simonjgreen/OpenObservatory-GardenInk/art_studio/reference/robin.png

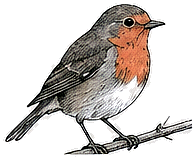
art_studio/reference/robin.png
