simonjgreen/OpenObservatory-GardenInk/design/concepts/04-selected-editorial-target.png

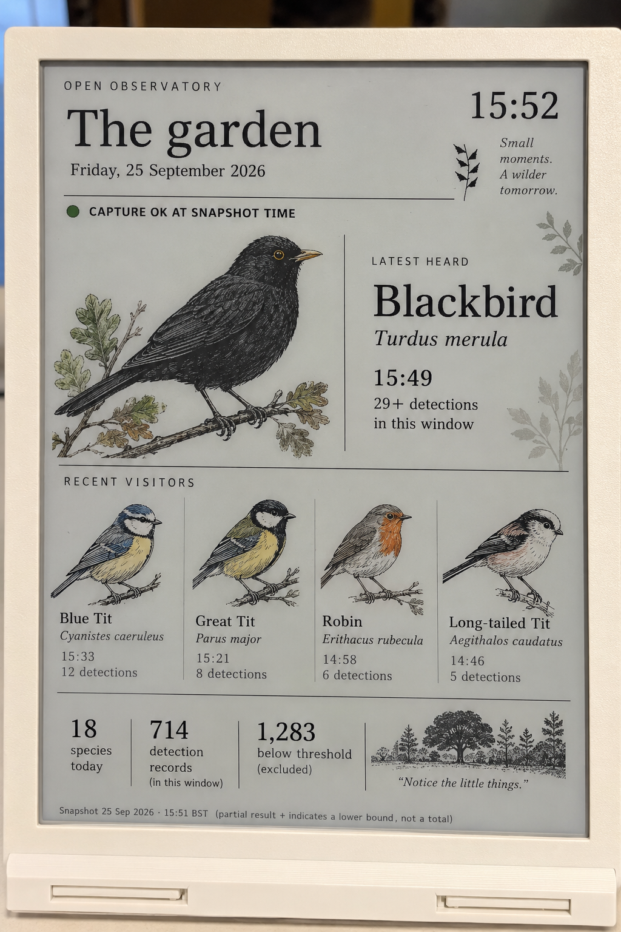
design/concepts/04-selected-editorial-target.png
