simonjgreen/OpenObservatory-GardenInk/design/concepts/after-dark-2026-09-27/01-night-rhythm.png

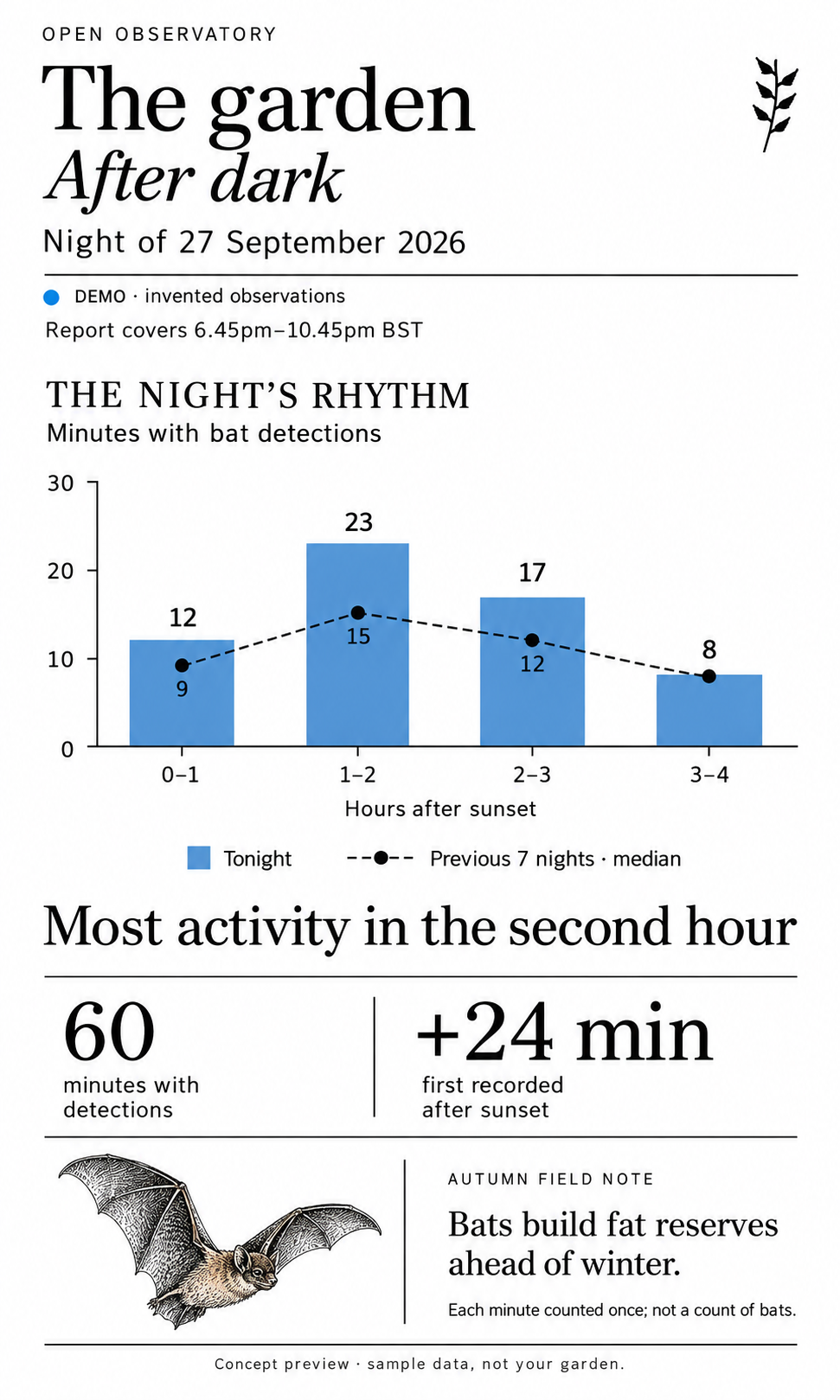
design/concepts/after-dark-2026-09-27/01-night-rhythm.png
