simonjgreen/OpenObservatory-GardenInk/design/concepts/after-dark-2026-09-27/02-seven-nights.png

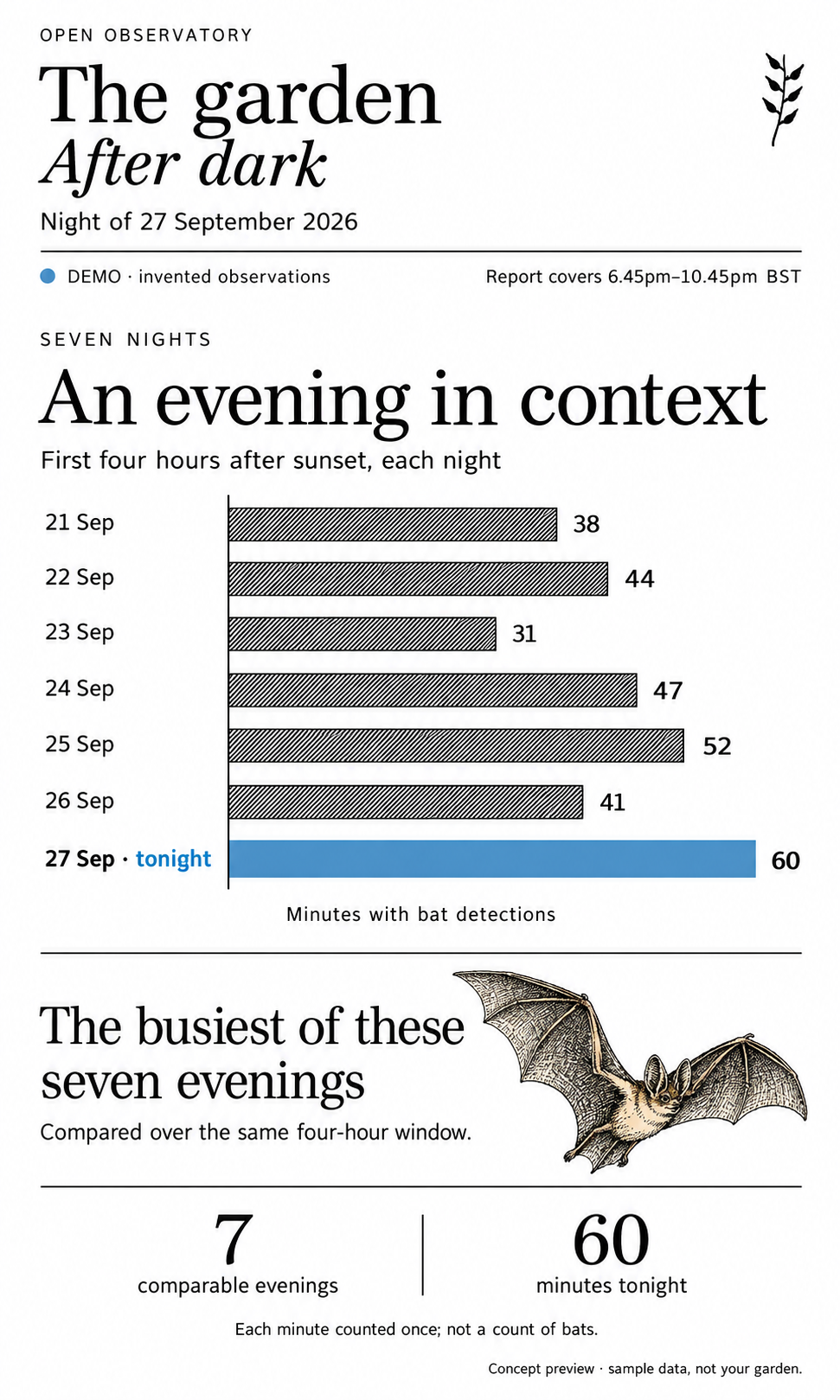
design/concepts/after-dark-2026-09-27/02-seven-nights.png
