simonjgreen/OpenObservatory-GardenInk/design/concepts/after-dark-bats-and-owls-v3/01-night-rhythm.png

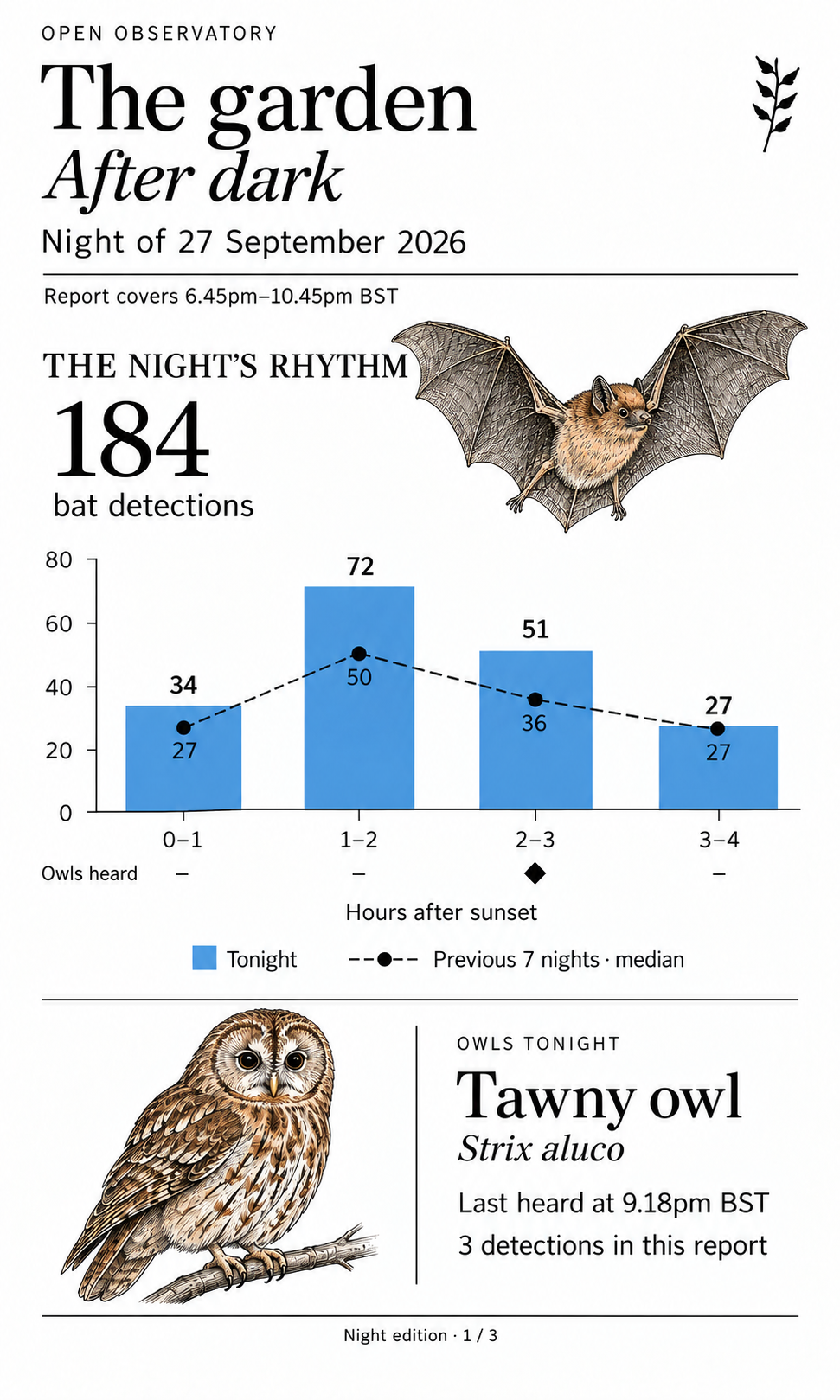
design/concepts/after-dark-bats-and-owls-v3/01-night-rhythm.png
