simonjgreen/OpenObservatory-GardenInk/design/concepts/after-dark-bats-and-owls-v3/02-seven-nights.png

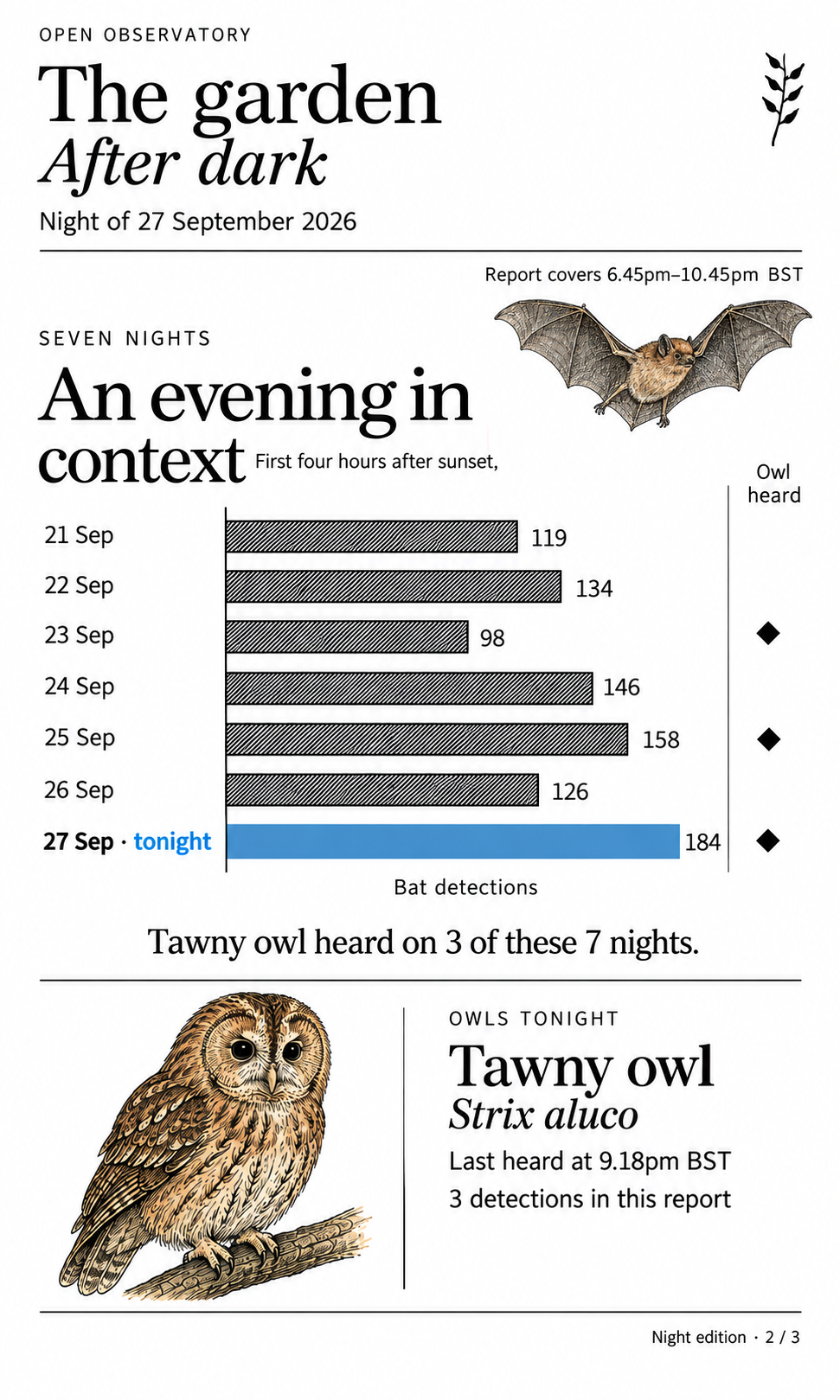
design/concepts/after-dark-bats-and-owls-v3/02-seven-nights.png
