simonjgreen/OpenObservatory-GardenInk/design/concepts/after-dark-owls-2026-09-27/01-night-rhythm-with-owl.png

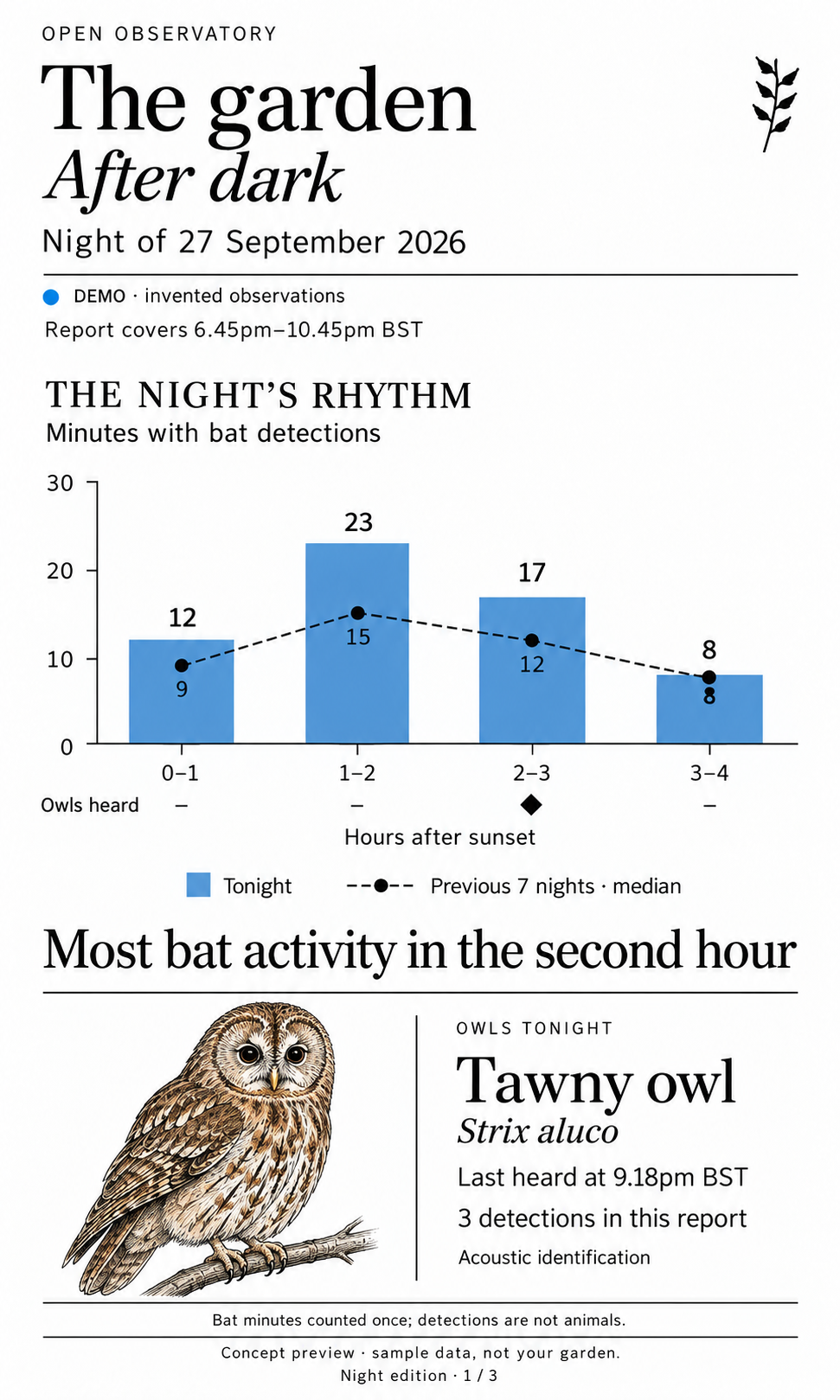
design/concepts/after-dark-owls-2026-09-27/01-night-rhythm-with-owl.png
