simonjgreen/OpenObservatory-GardenInk/design/concepts/after-dark-owls-2026-09-27/02-seven-nights-with-owl.png

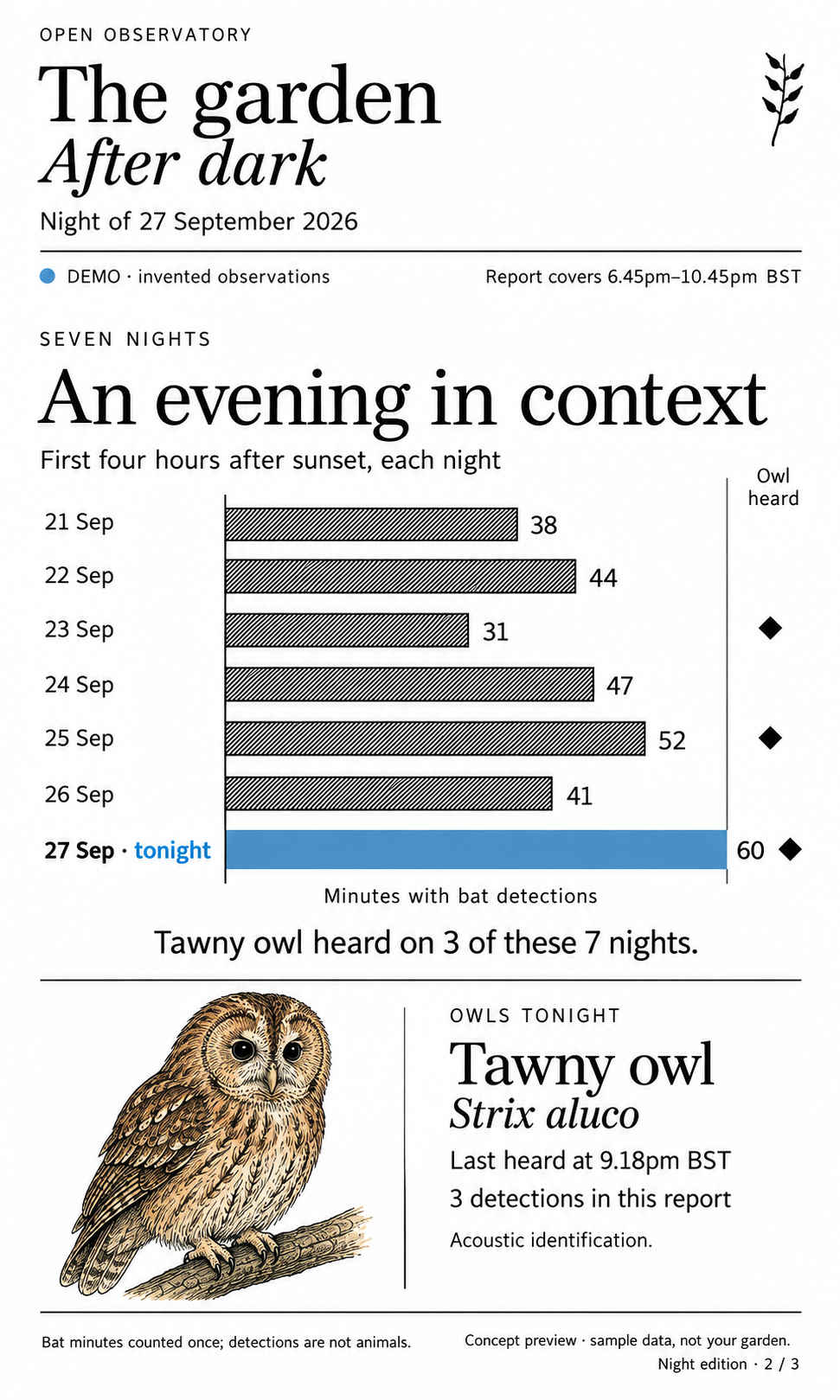
design/concepts/after-dark-owls-2026-09-27/02-seven-nights-with-owl.png
