simonjgreen/OpenObservatory-GardenInk/design/previews/after-dark/night-rhythm.png

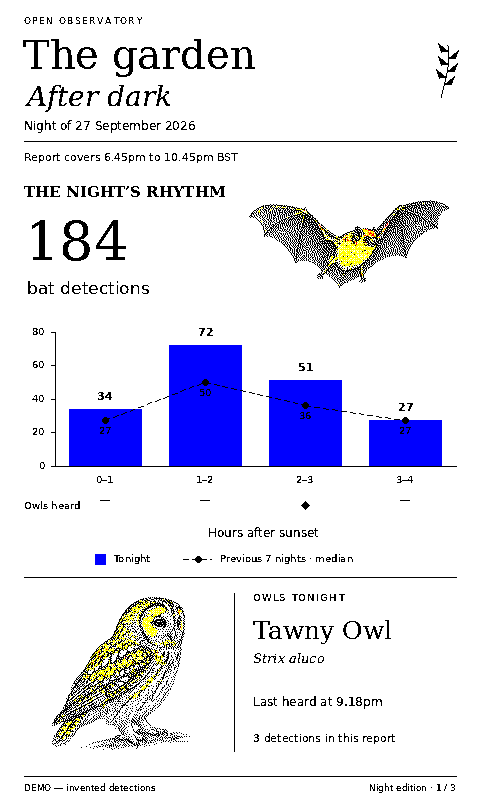
design/previews/after-dark/night-rhythm.png
