simonjgreen/OpenObservatory-GardenInk/design/previews/v2.1/no_clock.png

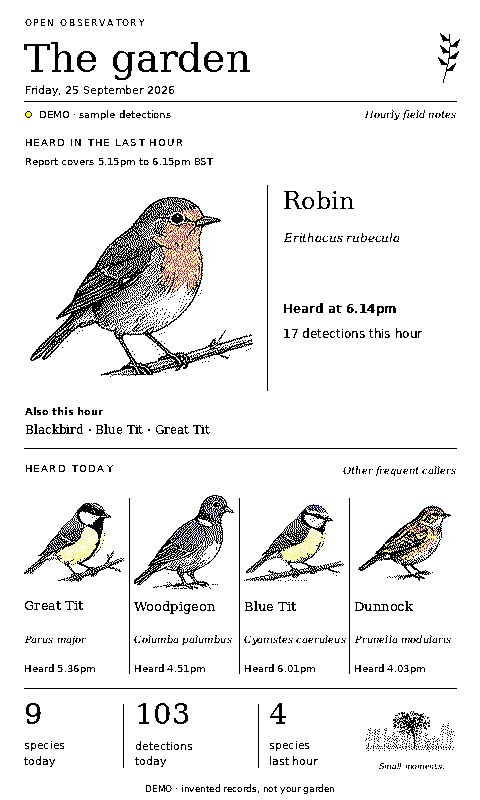
design/previews/v2.1/no_clock.png
