simonjgreen/OpenObservatory-GardenInk/display/assets/birds/aegithalos_caudatus.png

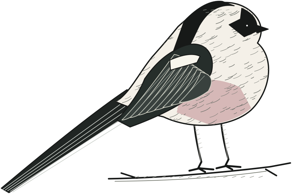
display/assets/birds/aegithalos_caudatus.png
