simonjgreen/OpenObservatory-GardenInk/display/assets/birds/alcedo_atthis.png

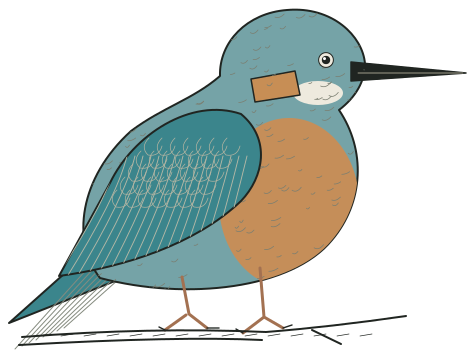
display/assets/birds/alcedo_atthis.png
