simonjgreen/OpenObservatory-GardenInk/display/assets/birds/anas_platyrhynchos.png

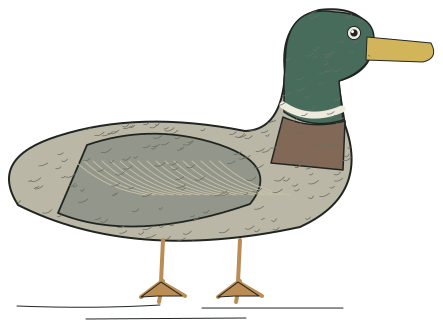
display/assets/birds/anas_platyrhynchos.png
