simonjgreen/OpenObservatory-GardenInk/display/assets/birds/ardea_cinerea.png

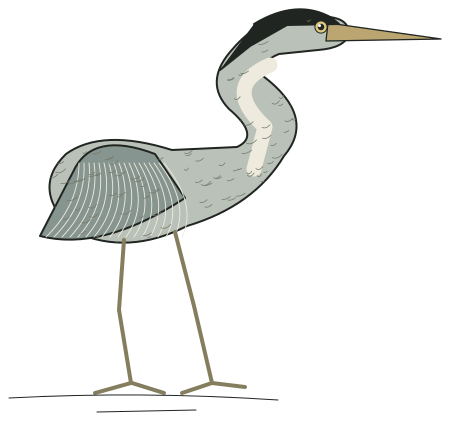
display/assets/birds/ardea_cinerea.png
