simonjgreen/OpenObservatory-GardenInk/display/assets/birds/branta_canadensis.png

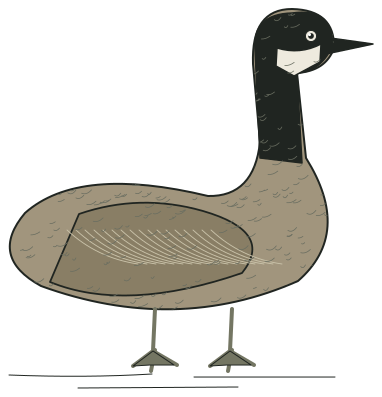
display/assets/birds/branta_canadensis.png
