simonjgreen/OpenObservatory-GardenInk/display/assets/birds/buteo_buteo.png

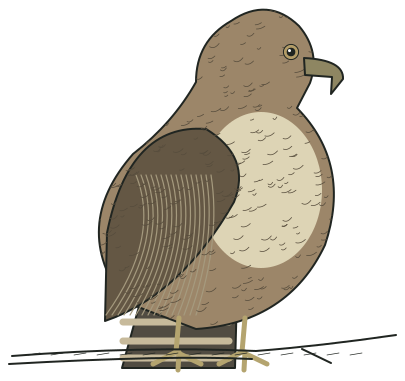
display/assets/birds/buteo_buteo.png
