simonjgreen/OpenObservatory-GardenInk/display/assets/birds/chloris_chloris.png

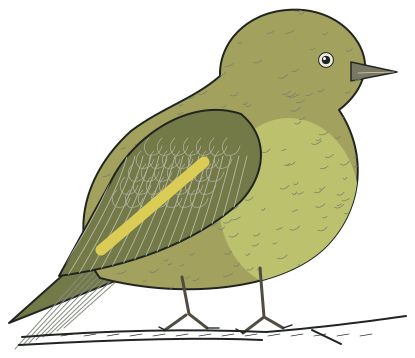
display/assets/birds/chloris_chloris.png
