simonjgreen/OpenObservatory-GardenInk/display/assets/birds/columba_livia.png

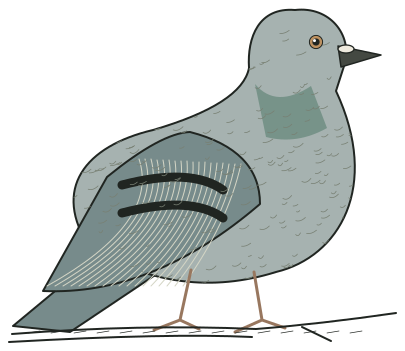
display/assets/birds/columba_livia.png
