simonjgreen/OpenObservatory-GardenInk/display/assets/birds/columba_palumbus.png

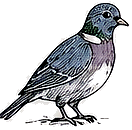
display/assets/birds/columba_palumbus.png
