simonjgreen/OpenObservatory-GardenInk/display/assets/birds/corvus_corax.png

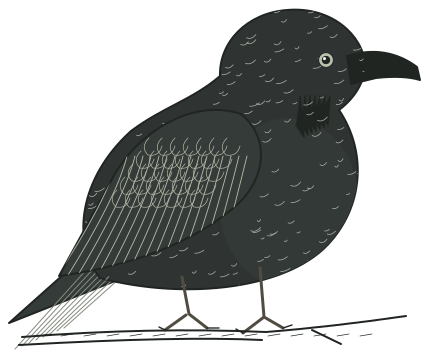
display/assets/birds/corvus_corax.png
