simonjgreen/OpenObservatory-GardenInk/display/assets/birds/corvus_corone.png

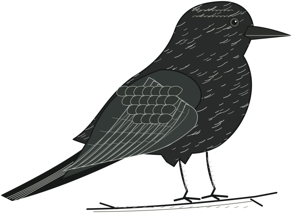
display/assets/birds/corvus_corone.png
