simonjgreen/OpenObservatory-GardenInk/display/assets/birds/cyanistes_caeruleus.png

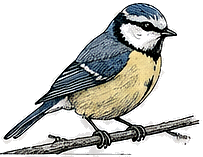
display/assets/birds/cyanistes_caeruleus.png
