simonjgreen/OpenObservatory-GardenInk/display/assets/birds/delichon_urbicum.png

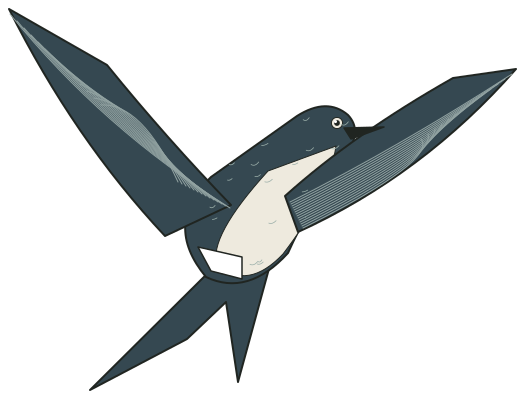
display/assets/birds/delichon_urbicum.png
