simonjgreen/OpenObservatory-GardenInk/display/assets/birds/dendrocopos_major.png

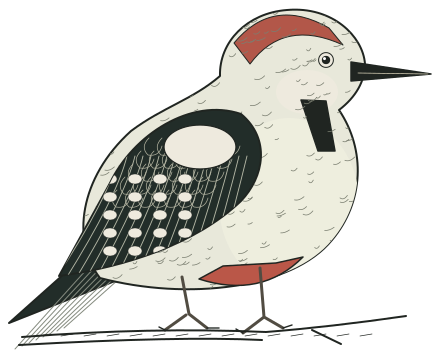
display/assets/birds/dendrocopos_major.png
