simonjgreen/OpenObservatory-GardenInk/display/assets/birds/fulica_atra.png

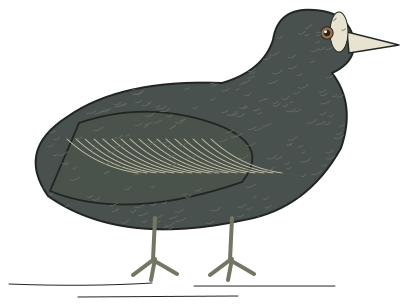
display/assets/birds/fulica_atra.png
