simonjgreen/OpenObservatory-GardenInk/display/assets/birds/garrulus_glandarius.png

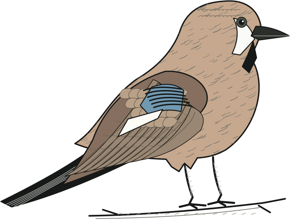
display/assets/birds/garrulus_glandarius.png
