simonjgreen/OpenObservatory-GardenInk/display/assets/birds/milvus_milvus.png

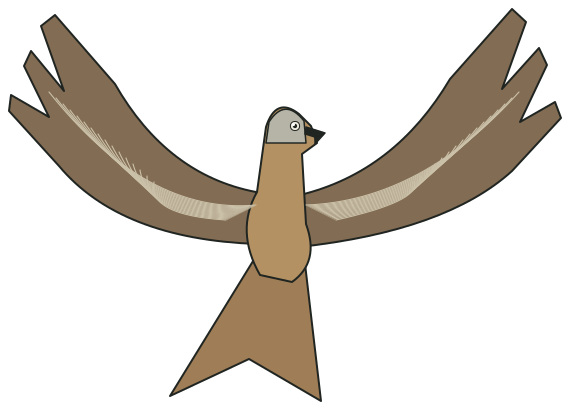
display/assets/birds/milvus_milvus.png
