simonjgreen/OpenObservatory-GardenInk/display/assets/birds/motacilla_alba.png

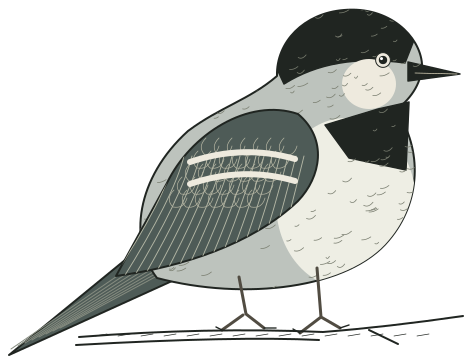
display/assets/birds/motacilla_alba.png
