simonjgreen/OpenObservatory-GardenInk/display/assets/birds/motacilla_cinerea.png

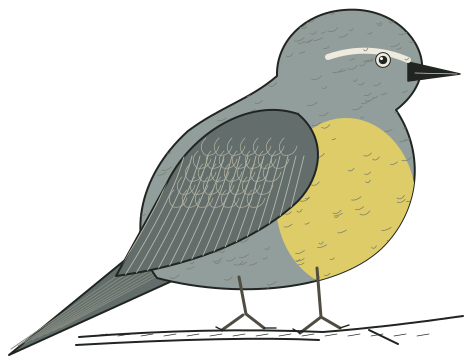
display/assets/birds/motacilla_cinerea.png
