simonjgreen/OpenObservatory-GardenInk/display/assets/birds/muscicapa_striata.png

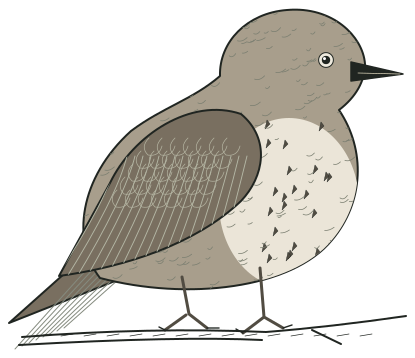
display/assets/birds/muscicapa_striata.png
