simonjgreen/OpenObservatory-GardenInk/display/assets/birds/parus_major.png

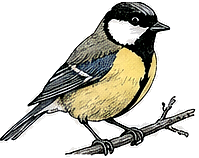
display/assets/birds/parus_major.png
