simonjgreen/OpenObservatory-GardenInk/display/assets/birds/passer_domesticus.png

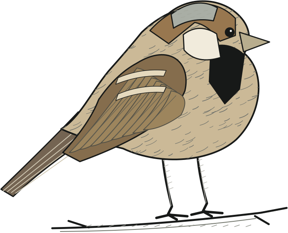
display/assets/birds/passer_domesticus.png
