simonjgreen/OpenObservatory-GardenInk/display/assets/birds/periparus_ater.png

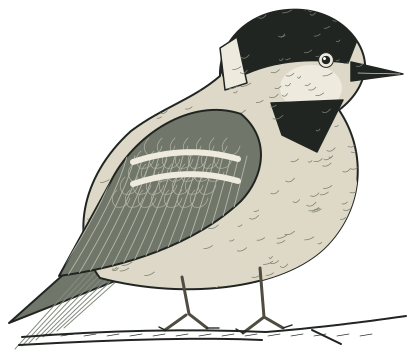
display/assets/birds/periparus_ater.png
