simonjgreen/OpenObservatory-GardenInk/display/assets/birds/phasianus_colchicus.png

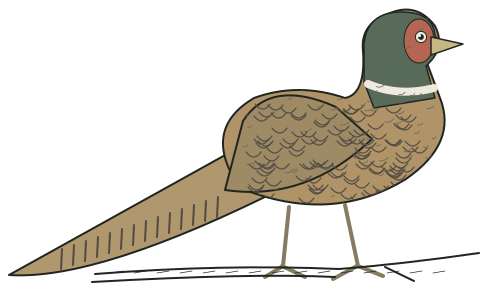
display/assets/birds/phasianus_colchicus.png
