simonjgreen/OpenObservatory-GardenInk/display/assets/birds/pica_pica.png

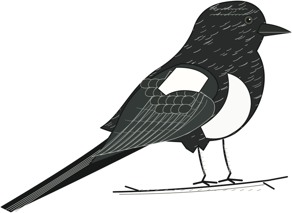
display/assets/birds/pica_pica.png
