simonjgreen/OpenObservatory-GardenInk/display/assets/birds/picus_viridis.png

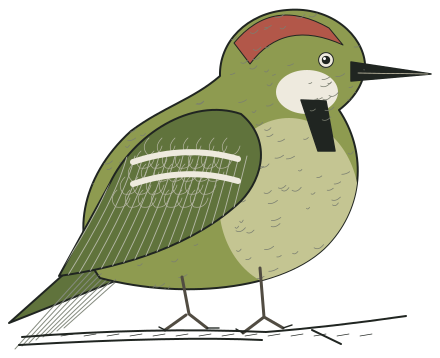
display/assets/birds/picus_viridis.png
