simonjgreen/OpenObservatory-GardenInk/display/assets/birds/porzana_porzana.png

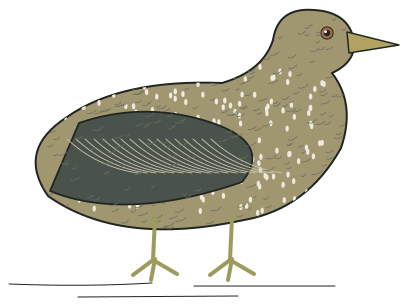
display/assets/birds/porzana_porzana.png
