simonjgreen/OpenObservatory-GardenInk/display/assets/birds/sitta_europaea.png

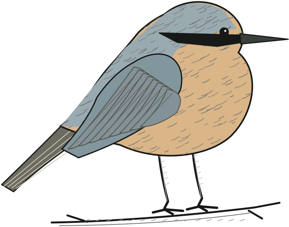
display/assets/birds/sitta_europaea.png
