simonjgreen/OpenObservatory-GardenInk/display/assets/birds/streptopelia_decaocto.png

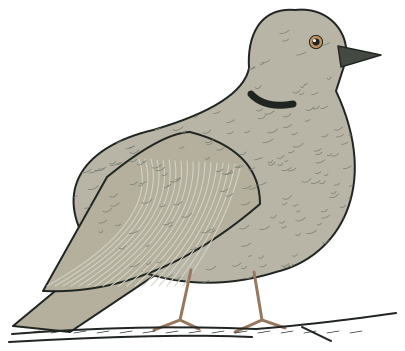
display/assets/birds/streptopelia_decaocto.png
