simonjgreen/OpenObservatory-GardenInk/display/assets/birds/strix_aluco.png

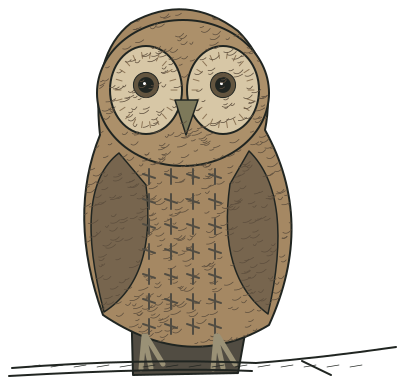
display/assets/birds/strix_aluco.png
