simonjgreen/OpenObservatory-GardenInk/display/assets/birds/turdus_merula.png

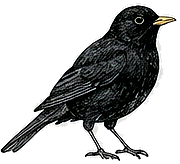
display/assets/birds/turdus_merula.png
