simonjgreen/OpenObservatory-GardenInk/display/assets/night/bat.png

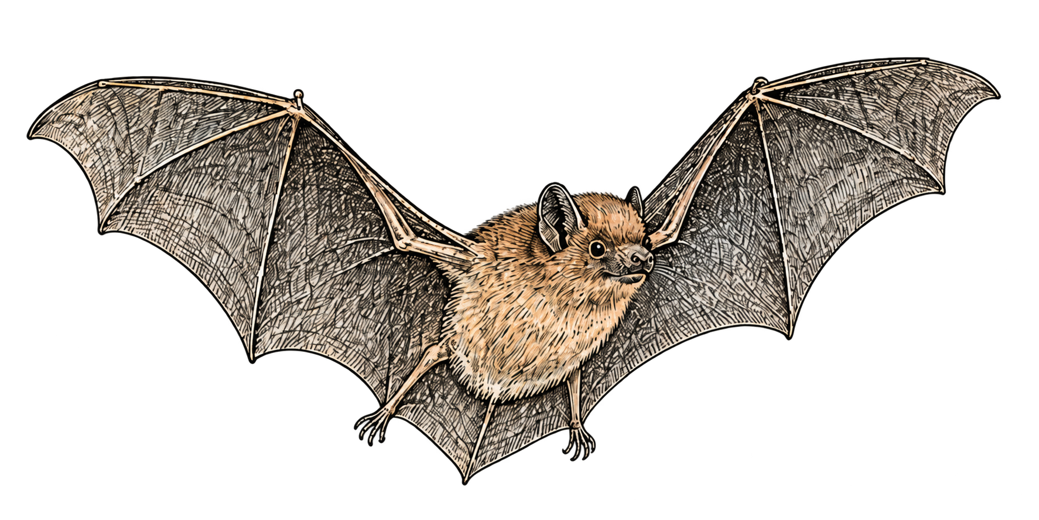
display/assets/night/bat.png
