simonjgreen/OpenObservatory-GardenInk/hardware/counterframe/reference/glass.stl

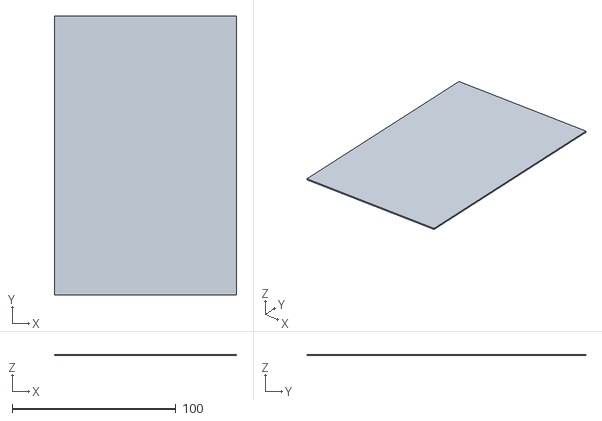
[picture p66: CAD file, 2026-09-26]
hardware/counterframe/reference/glass.stl
111.2 x 170.2 x 0.91
