simonjgreen/OpenObservatory-GardenInk/hardware/counterframe/stl/release_key.stl

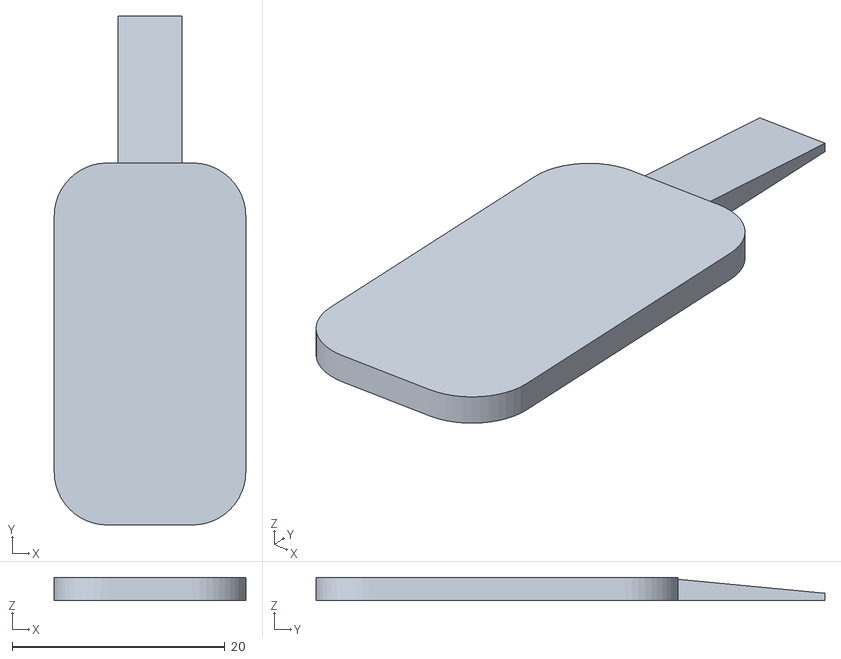
[picture p67: CAD file, 2026-09-26]
hardware/counterframe/stl/release_key.stl
18.0 x 47.8 x 2.20
