simonjgreen/OpenObservatory-GardenInk/hardware/counterframe/reference/hat_pcb.stl

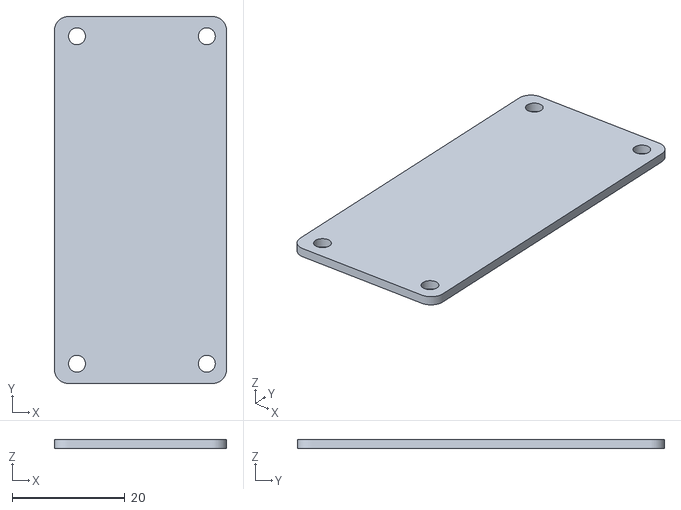
[picture p68: CAD file, 2026-09-26]
hardware/counterframe/reference/hat_pcb.stl
30.5 x 65.0 x 1.60
