simonjgreen/OpenObservatory-GardenInk/hardware/counterframe/stl/rear.stl

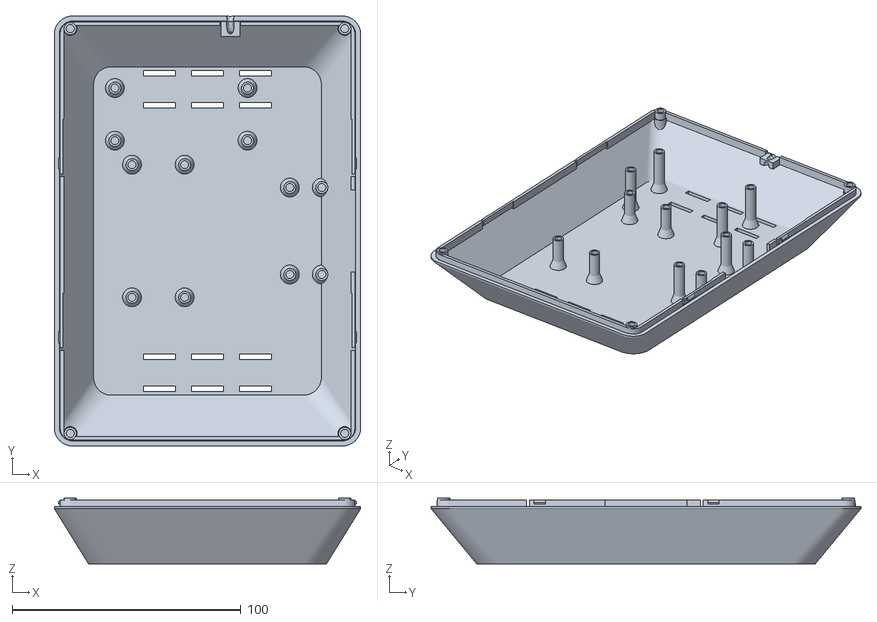
[picture p69: CAD file, 2026-09-26]
hardware/counterframe/stl/rear.stl
134.0 x 188.0 x 28.8
