simonjgreen/OpenObservatory-GardenInk/hardware/counterframe/checks/carrier_rear.scad

include <../counterframe.scad>
intersection(){ carrier_native(); rear_native(); }
