simonjgreen/OpenObservatory-GardenInk/hardware/counterframe/checks/front_carrier.scad

include <../counterframe.scad>
intersection(){ front_native(); carrier_native(); }
