simonjgreen/OpenObservatory-GardenInk/hardware/counterframe/checks/front_rear.scad

include <../counterframe.scad>
intersection(){ front_native(); rear_native(); }
