simonjgreen/OpenObservatory-GardenInk/hardware/counterframe/checks/render_adapter_pcb.scad

include <../counterframe.scad>
pcb(adapter_pos,adapter_size,adapter_z,adapter_holes,3,[.1,.2,.4]);
