simonjgreen/OpenObservatory-GardenInk/hardware/counterframe/checks/render_ffc.scad

include <../counterframe.scad>
ribbon_path(ffc_points,25.5,.18);
