simonjgreen/OpenObservatory-GardenInk/hardware/counterframe/checks/render_fpc.scad

include <../counterframe.scad>
ribbon_path(fpc_points,25.5,.15);
