simonjgreen/OpenObservatory-GardenInk/hardware/counterframe/checks/render_hat_pcb.scad

include <../counterframe.scad>
pcb(hat_pos,hat_size,hat_z,hat_holes,3,[.1,.2,.4]);
