simonjgreen/OpenObservatory-GardenInk/hardware/counterframe/checks/render_pi_pcb.scad

include <../counterframe.scad>
pcb(pi_pos,pi_size,pi_z,pi_holes,2.75,[.1,.3,.2]);
