simonjgreen/OpenObservatory-GardenInk/hardware/counterframe/checks/render_power_external.scad

include <../counterframe.scad>
power_external();
