simonjgreen/OpenObservatory-GardenInk/hardware/counterframe/checks/render_wires.scad

include <../counterframe.scad>
wires_native();
