simonjgreen/OpenObservatory-GardenInk/hardware/counterframe/checks/ribbon_carrier.scad

include <../counterframe.scad>
intersection(){ ribbons_native(); carrier_native(); }
