simonjgreen/OpenObservatory-GardenInk/hardware/counterframe/checks/ribbon_front.scad

include <../counterframe.scad>
intersection(){ ribbons_native(); front_native(); }
