simonjgreen/OpenObservatory-GardenInk/hardware/counterframe/checks/ribbon_rear.scad

include <../counterframe.scad>
intersection(){ ribbons_native(); rear_native(); }
