simonjgreen/OpenObservatory-GardenInk/hardware/counterframe/checks/usb_stand.scad

include <../counterframe.scad>
intersection(){ stand_native(); standing() wires_native(); }
