simonjgreen/OpenObservatory-GardenInk/hardware/counterframe/checks/wires_carrier.scad

include <../counterframe.scad>
intersection(){ wires_native(); carrier_native(); }
