simonjgreen/OpenObservatory-GardenInk/hardware/counterframe/checks/wires_rear.scad

include <../counterframe.scad>
intersection(){ wires_native(); rear_native(); }
