simonjgreen/OpenObservatory-GardenInk/design/concepts/after-dark-2026-09-27/03-bat-field-journal.png

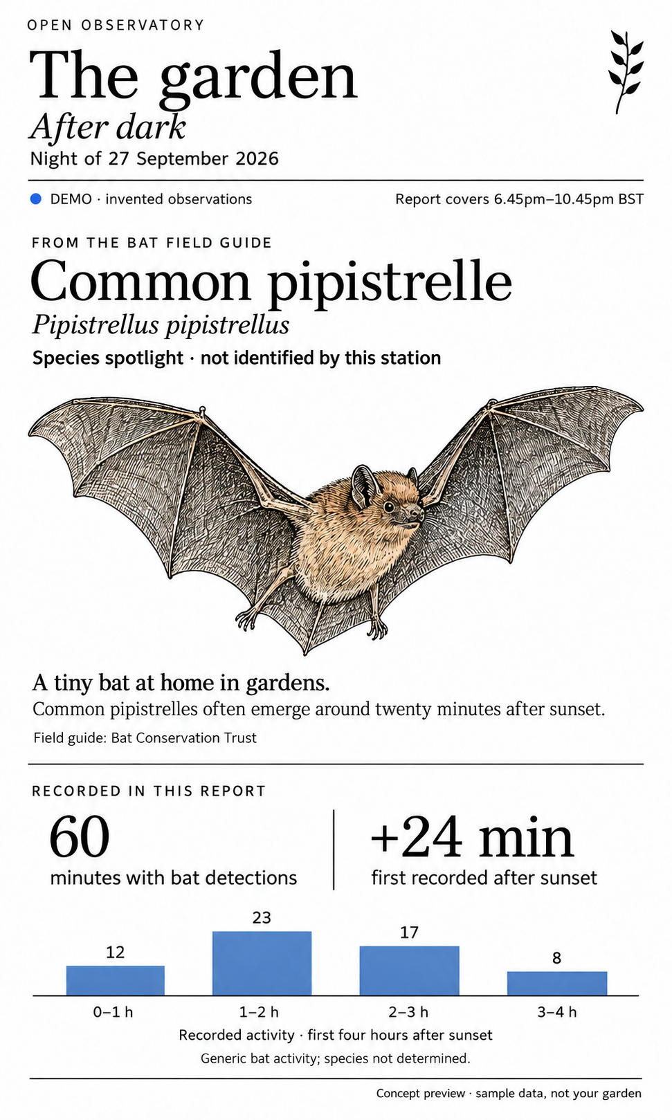
design/concepts/after-dark-2026-09-27/03-bat-field-journal.png
