simonjgreen/OpenObservatory-GardenInk/design/concepts/after-dark-bats-and-owls-v3/03-night-field-journal.png

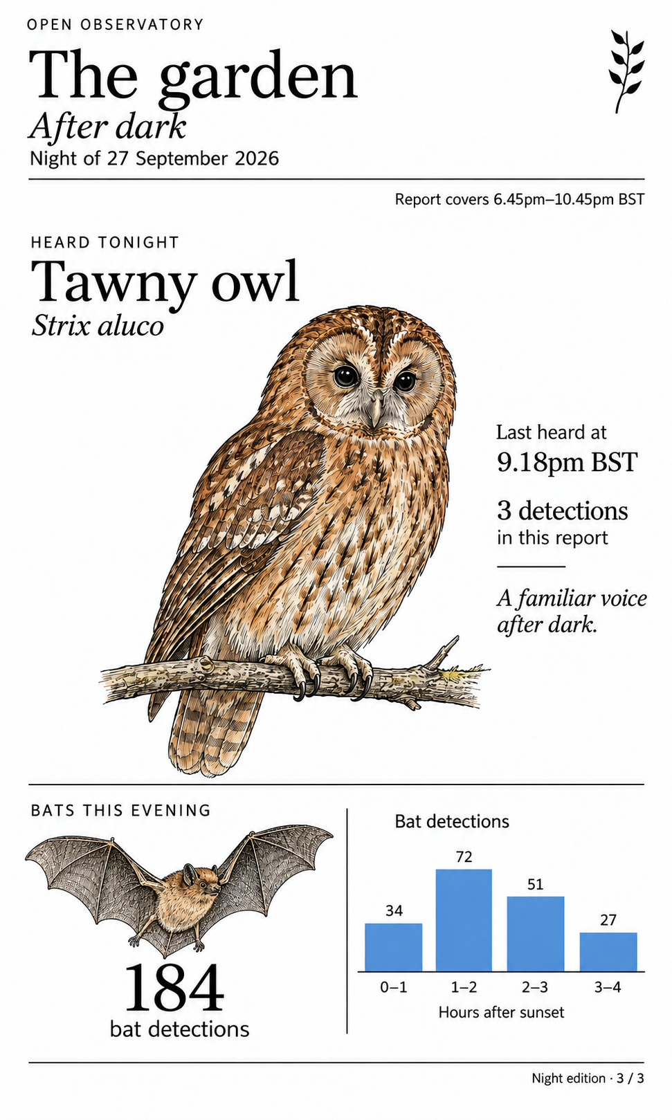
design/concepts/after-dark-bats-and-owls-v3/03-night-field-journal.png
