simonjgreen/OpenObservatory-GardenInk/design/concepts/after-dark-owls-2026-09-27/03-owl-field-journal.png

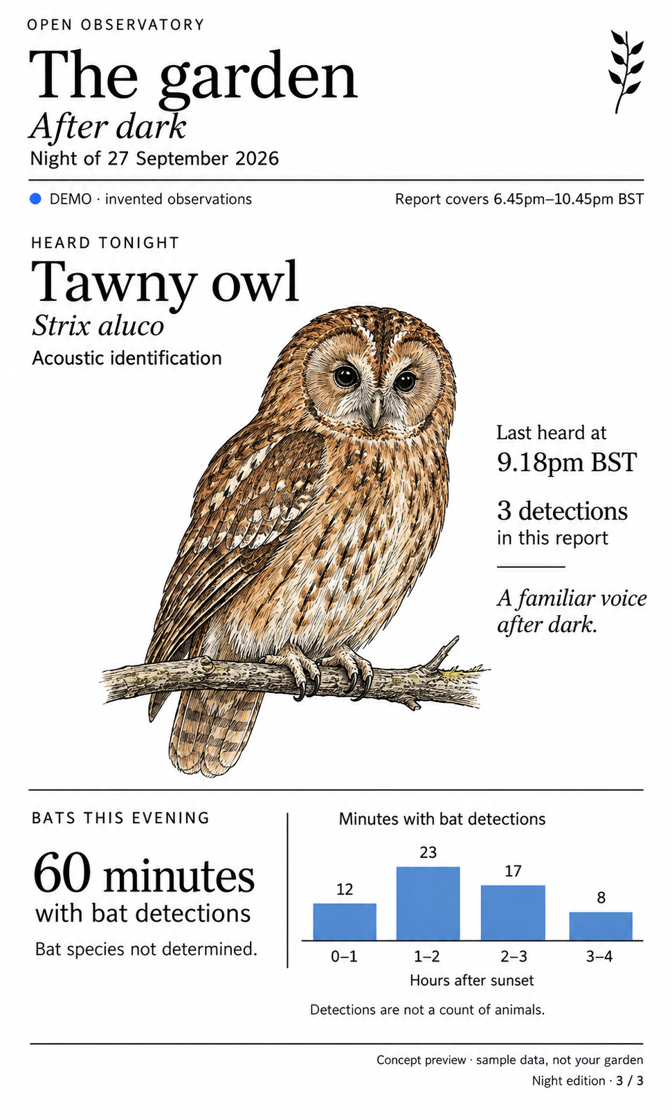
design/concepts/after-dark-owls-2026-09-27/03-owl-field-journal.png
