simonjgreen/OpenObservatory-GardenInk/design/previews/after-dark/night-history.png

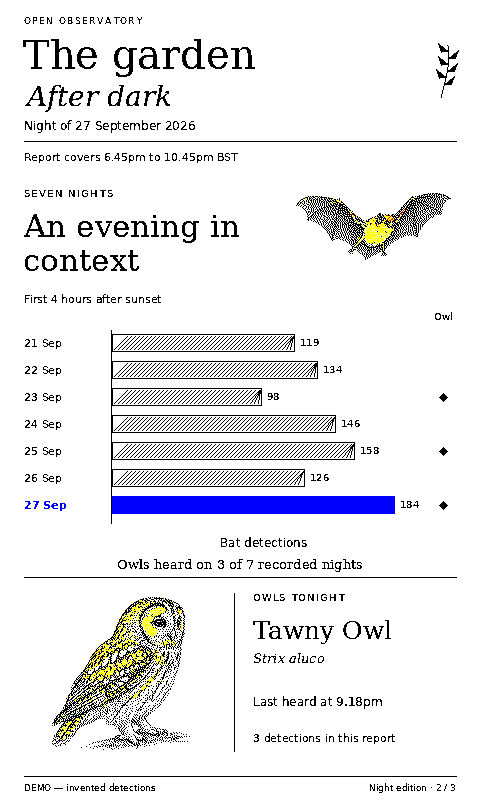
design/previews/after-dark/night-history.png
