simonjgreen/OpenObservatory-GardenInk/design/previews/after-dark/night-journal.png

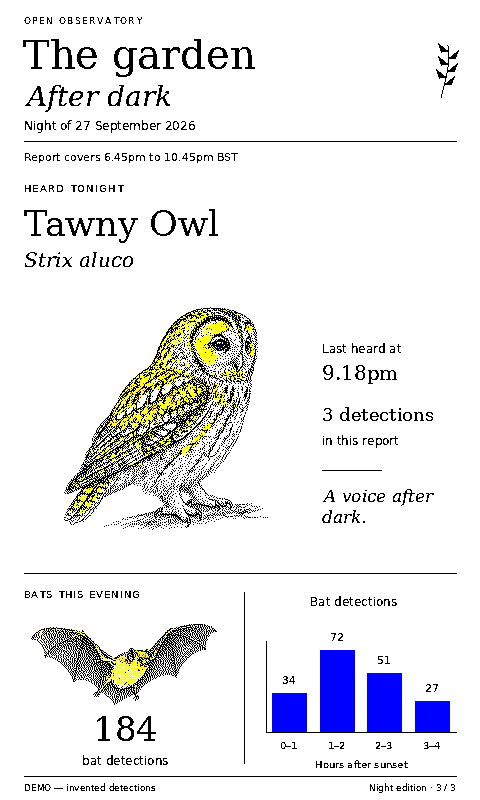
design/previews/after-dark/night-journal.png
